DmitriLyalikov/ESP32_Smart_Clock/components/http/include/http.h

#ifndef HTTP_H
#define HTTP_H

#ifdef __cplusplus
extern "C" {
#endif

#include "esp_err.h"

typedef void (*http_callback)(uint32_t *args);

typedef struct {
    char *recv_buf;     /*!< Pointer to a receive buffer, data from the socket are collected here */
    int recv_buf_size;  /*!< Size of the receive buffer */
    char *proc_buf;     /*!< Pointer to processing buffer,  chunks of data from receive buffer and collected here. */
    int proc_buf_size;  /*!< Size of processing buffer*/
    http_callback http_connected_cb;       /*!< Pointer to function called once socket connection is established  */
    http_callback http_process_chunk_cb;   /*!< Pointer to function called to process contents of receive buffer, once it is filled up */
    http_callback http_disconnected_cb;    /*!< Pointer to function called after disconnecting from the socket */
} http_client_data;

#define ESP_ERR_HTTP_BASE 0x40000
#define ESP_ERR_HTTP_DNS_LOOKUP_FAILED          (ESP_ERR_HTTP_BASE + 1)
#define ESP_ERR_HTTP_FAILED_TO_ALLOCATE_SOCKET  (ESP_ERR_HTTP_BASE + 2)
#define ESP_ERR_HTTP_SOCKET_CONNECT_FAILED      (ESP_ERR_HTTP_BASE + 3)
#define ESP_ERR_HTTP_SOCKET_SEND_FAILED         (ESP_ERR_HTTP_BASE + 4)

const char* find_response_body(char * response);
void http_client_on_connected(http_client_data *client, http_callback http_connected_cb);
void http_client_on_process_chunk(http_client_data *client, http_callback http_process_chunk_cb);
void http_client_on_disconnected(http_client_data *client, http_callback http_disconnected_cb);
esp_err_t http_client_request(http_client_data *client, const char *web_server, const char *request_string);


#ifdef __cplusplus
}
#endif

#endif
